AndreiTudorBurlacu/SmartWatch-Design/Images/EPD_Display.png

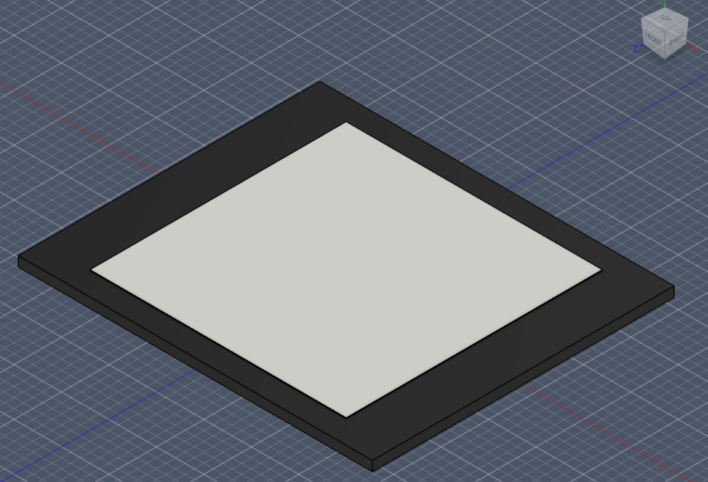
Images/EPD_Display.png
