AndreiTudorBurlacu/SmartWatch-Design/Images/HapticMototr.png

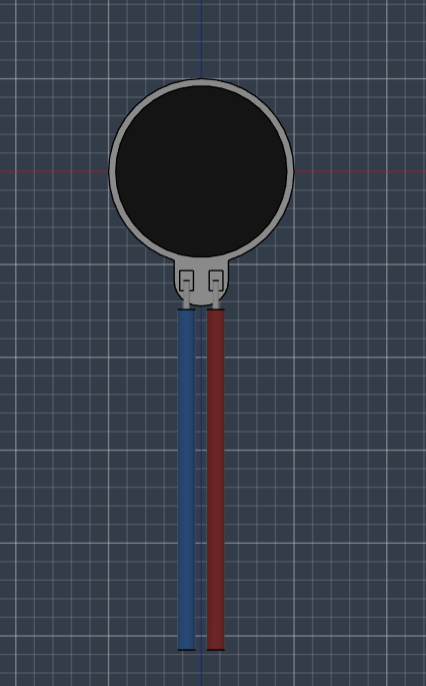
Images/HapticMototr.png
